Bob-vdV/floating-hub-cap/fast_dome.scad

./centercap/fast_dome.scad
