Bob-vdV/floating-hub-cap/key.scad

./centercap/key.scad
