Bob-vdV/floating-hub-cap/ribbed_hole.scad

./centercap/ribbed_hole.scad
