Bob-vdV/floating-hub-cap/swing_screws.scad

./centercap/swing_screws.scad
