Bob-vdV/floating-hub-cap/top_plain.scad

./centercap/top_plain.scad
