Bob-vdV/floating-hub-cap/top_vw_curved.scad

./centercap/top_vw_curved.scad
