Bob-vdV/floating-hub-cap/top_vw_flat.scad

./centercap/top_vw_flat.scad
