Bob-vdV/floating-hub-cap/vw.scad

./centercap/vw.scad
