Bob-vdV/floating-hub-cap/centercap/top_curved.scad

include <top_plain.scad>
include <fast_dome.scad>

module CenterCapTopCurved() {
  CenterCapTopPlain();

  dome(d=endcap_outer_diam, h=dome_height);
}
