Bob-vdV/floating-hub-cap/hubcap_tester.scad

./centercap/hubcap_tester.scad
